max05210238/Infidex_176_V/STL/Lens mount/Classic Cone/CONE_lens_classic_BOARD.stl

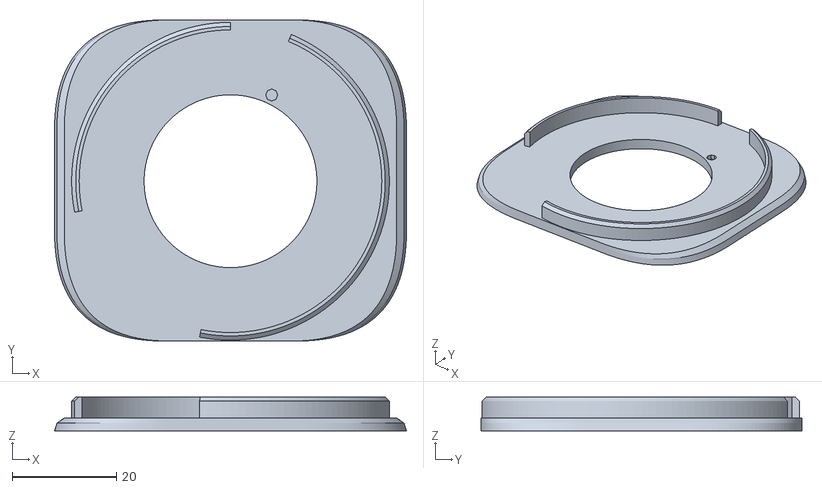
[picture p15: CAD file, 2026-06-08]
STL/Lens mount/Classic Cone/CONE_lens_classic_BOARD.stl
67.6 x 61.7 x 6.50
