max05210238/Infidex_176_V/STL/Lens mount/Focusing Helicoid/Helicoid_FOCUS_ring_ribs_shorter-2mm.stl

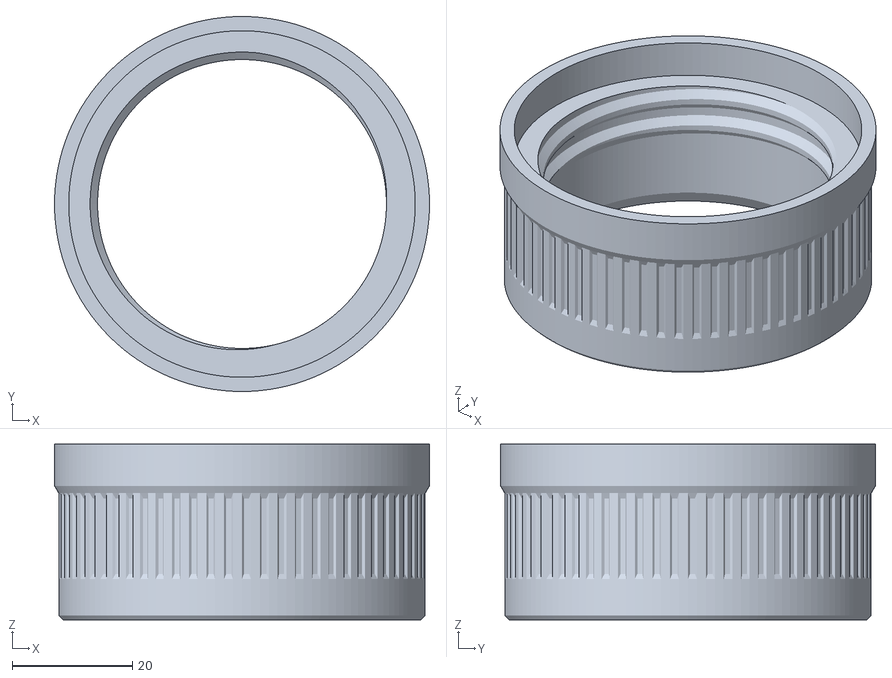
[picture p16: CAD file, 2026-06-08]
STL/Lens mount/Focusing Helicoid/Helicoid_FOCUS_ring_ribs_shorter-2mm.stl
62.4 x 62.4 x 29.2
