max05210238/Infidex_176_V/STL/Lens mount/Tube/Tube_Lens_BOARD.stl

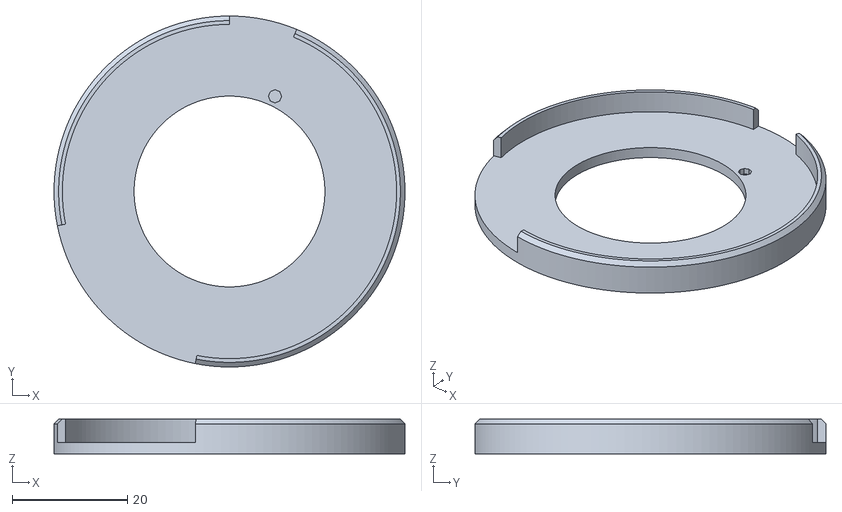
[picture p17: CAD file, 2026-06-08]
STL/Lens mount/Tube/Tube_Lens_BOARD.stl
61.0 x 61.0 x 6.00
