max05210238/Infidex_176_V/MODS/stl/Helicoid_MOUNT_BASE.stl

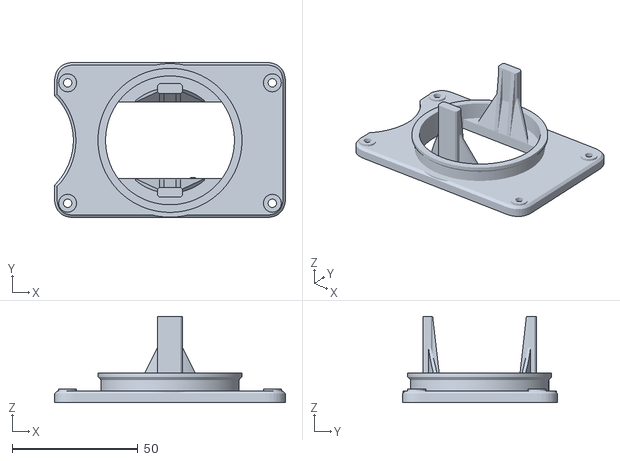
[picture p19: CAD file, 2026-06-08]
MODS/stl/Helicoid_MOUNT_BASE.stl
91.8 x 61.7 x 34.2
