max05210238/Infidex_176_V/STL/Body/BODY_top_ver2.stl

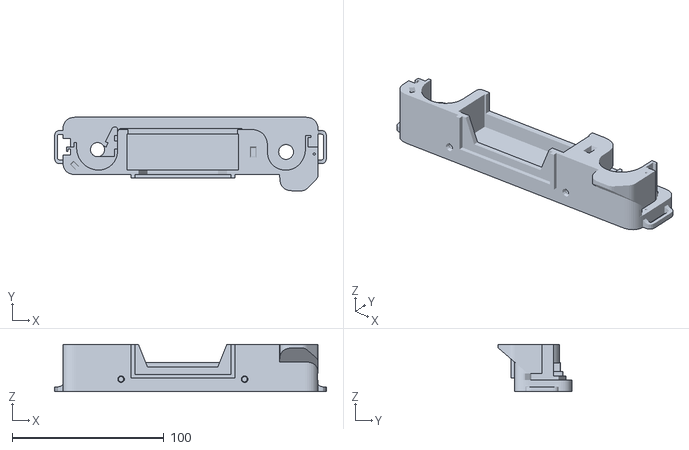
[picture p20: CAD file, 2026-06-08]
STL/Body/BODY_top_ver2.stl
179.0 x 48.5 x 31.0
