max05210238/Infidex_176_V/STL/Lens mount/Focusing Helicoid/Helicoid_INNER_ring_55mm (+0.5mm).stl

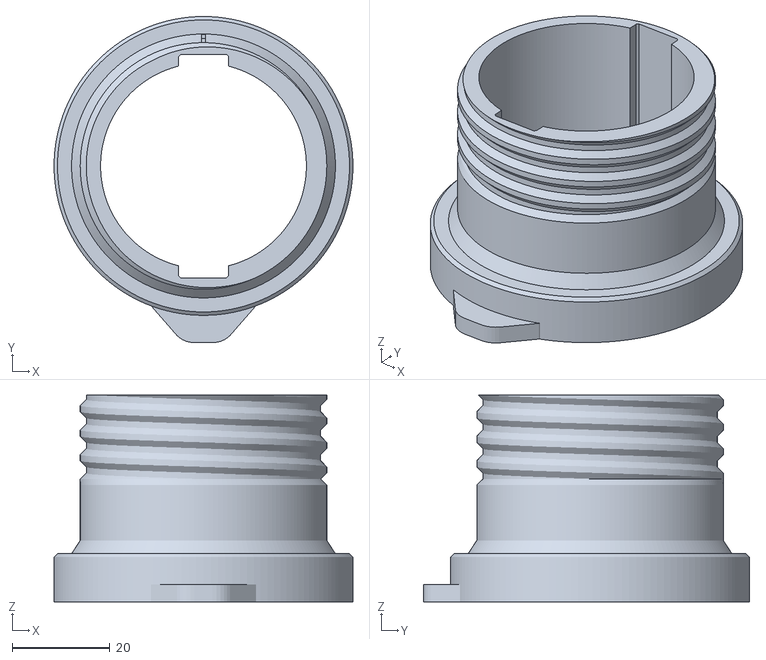
[picture p21: CAD file, 2026-06-08]
STL/Lens mount/Focusing Helicoid/Helicoid_INNER_ring_55mm (+0.5mm).stl
61.0 x 66.5 x 42.2
