max05210238/Infidex_176_V/STL/Small parts/Sprocket_gear_COUNTER.stl

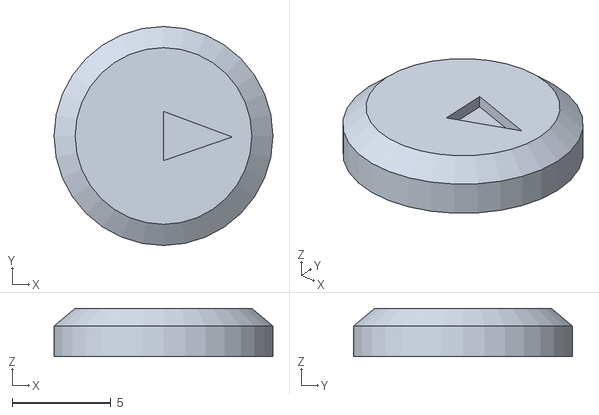
[picture p22: CAD file, 2026-06-08]
STL/Small parts/Sprocket_gear_COUNTER.stl
11.1 x 11.1 x 2.45
