max05210238/Infidex_176_V/MODS/stl/Door_v4.stl

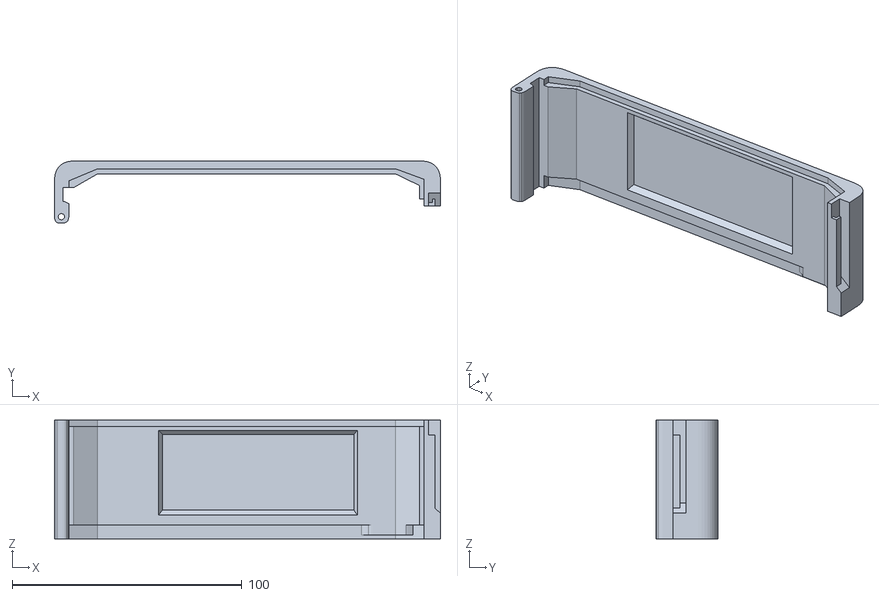
[picture p23: CAD file, 2026-06-08]
MODS/stl/Door_v4.stl
168.0 x 27.0 x 51.7
