max05210238/Infidex_176_V/STL/Body/BODY_bottom_ver2.stl

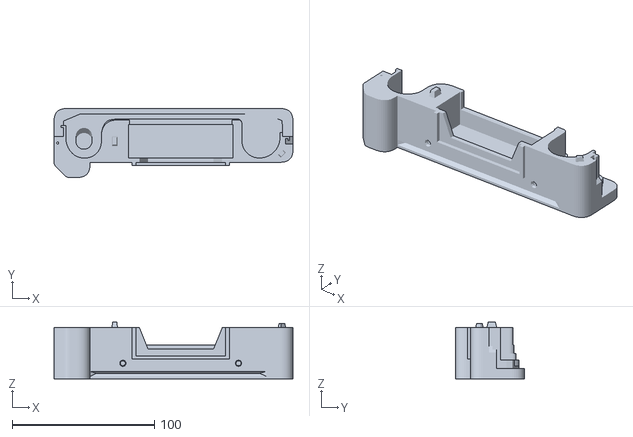
[picture p24: CAD file, 2026-06-08]
STL/Body/BODY_bottom_ver2.stl
168.0 x 48.5 x 40.0
