max05210238/Infidex_176_V/STL/Small parts/Viewfinder_var1_with_text.stl

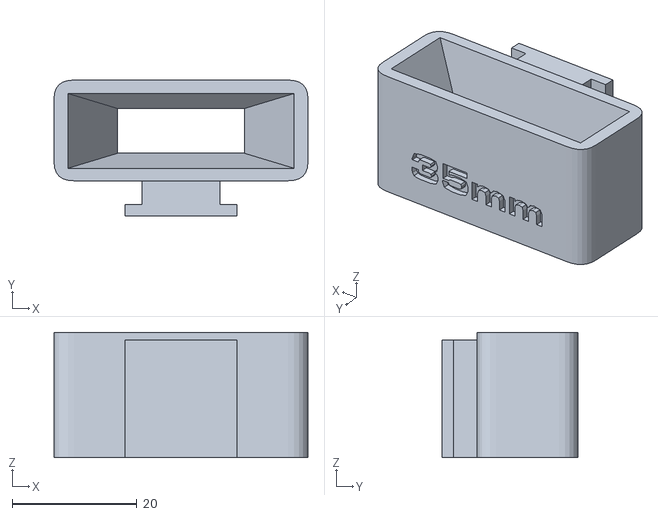
[picture p25: CAD file, 2026-06-08]
STL/Small parts/Viewfinder_var1_with_text.stl
40.7 x 21.8 x 20.1
