max05210238/Infidex_176_V/STL/Lens mount/Focusing Helicoid/Helicoid_FOCUS_ring_ribs.stl

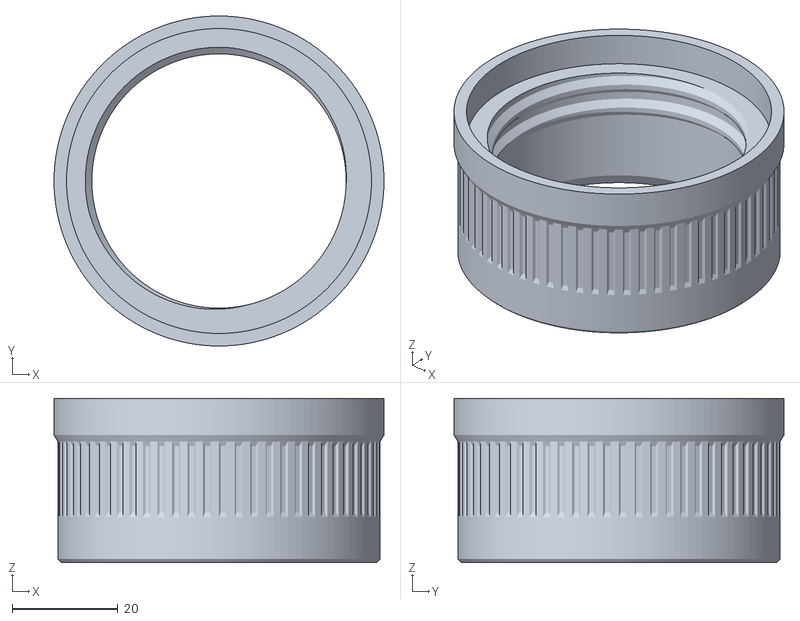
[picture p26: CAD file, 2026-06-08]
STL/Lens mount/Focusing Helicoid/Helicoid_FOCUS_ring_ribs.stl
62.4 x 62.4 x 31.1
