max05210238/Infidex_176_V/STL/Small parts/Winding_knob_var2.stl

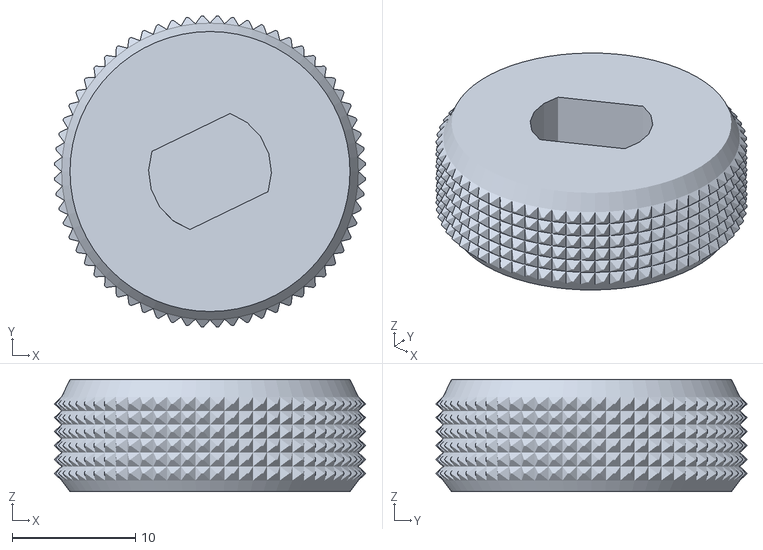
[picture p27: CAD file, 2026-06-08]
STL/Small parts/Winding_knob_var2.stl
25.2 x 25.2 x 9.10
