max05210238/Infidex_176_V/MODS/stl/Body_bottom.stl

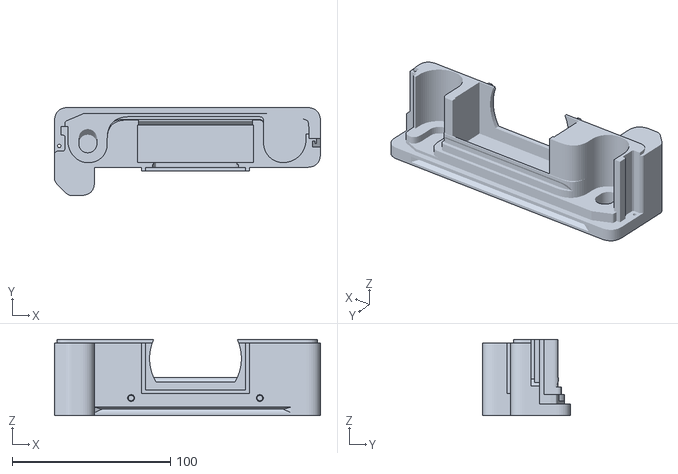
[picture p28: CAD file, 2026-06-08]
MODS/stl/Body_bottom.stl
168.0 x 55.6 x 48.0
