max05210238/Infidex_176_V/STL/Body/Door_var3.stl

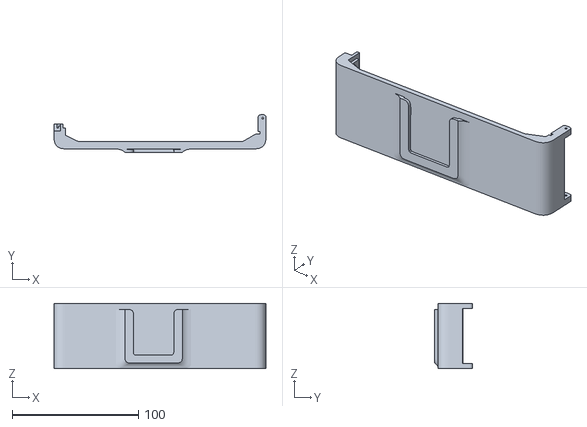
[picture p29: CAD file, 2026-06-08]
STL/Body/Door_var3.stl
168.0 x 29.8 x 51.7
