max05210238/Infidex_176_V/STL/Lens mount/Focusing Helicoid/Helicoid_INNER_ring_80mm_shorter-2mm.stl

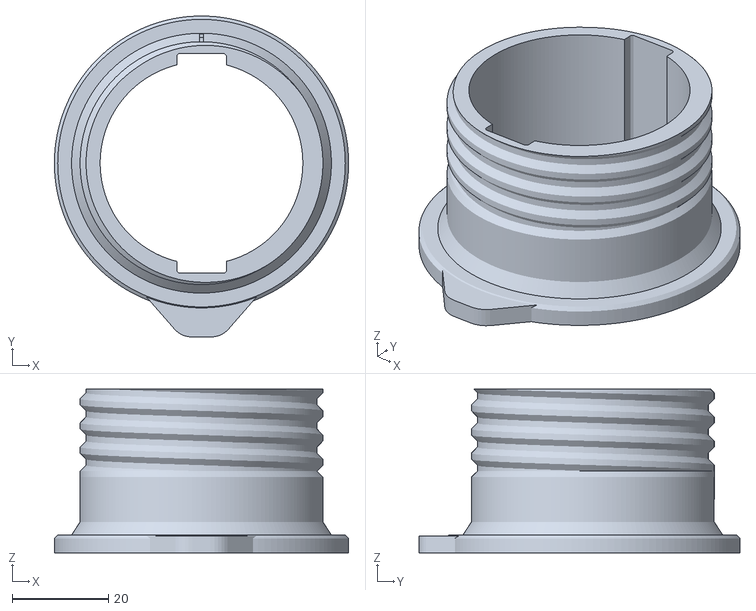
[picture p30: CAD file, 2026-06-08]
STL/Lens mount/Focusing Helicoid/Helicoid_INNER_ring_80mm_shorter-2mm.stl
61.0 x 66.5 x 34.0
