max05210238/Infidex_176_V/STL/Small parts/Latch.stl

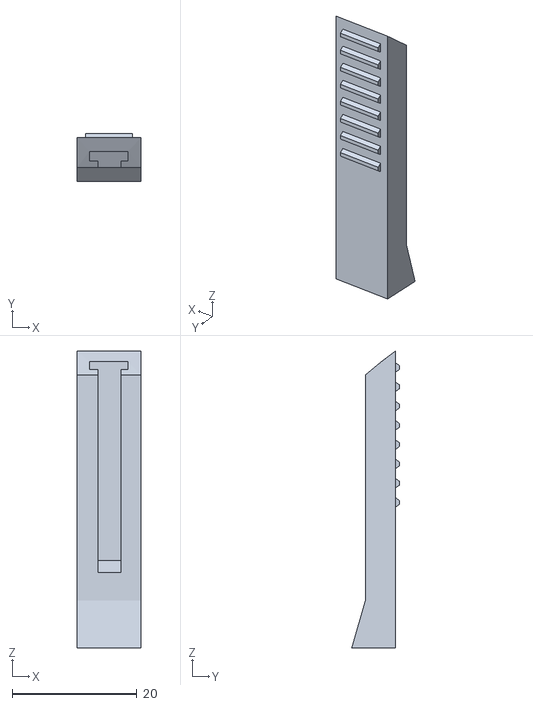
[picture p31: CAD file, 2026-06-08]
STL/Small parts/Latch.stl
10.3 x 7.64 x 47.6
