max05210238/Infidex_176_V/STL/Body/Door_var1.stl

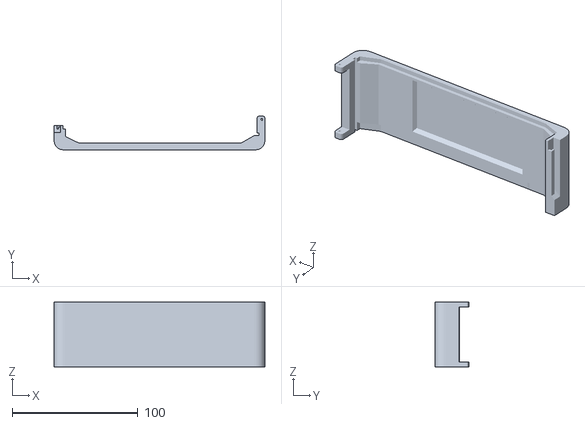
[picture p32: CAD file, 2026-06-08]
STL/Body/Door_var1.stl
168.0 x 27.0 x 51.7
