max05210238/Infidex_176_V/STL/Lens mount/Focusing Helicoid/Helicoid_FIX_ring.stl

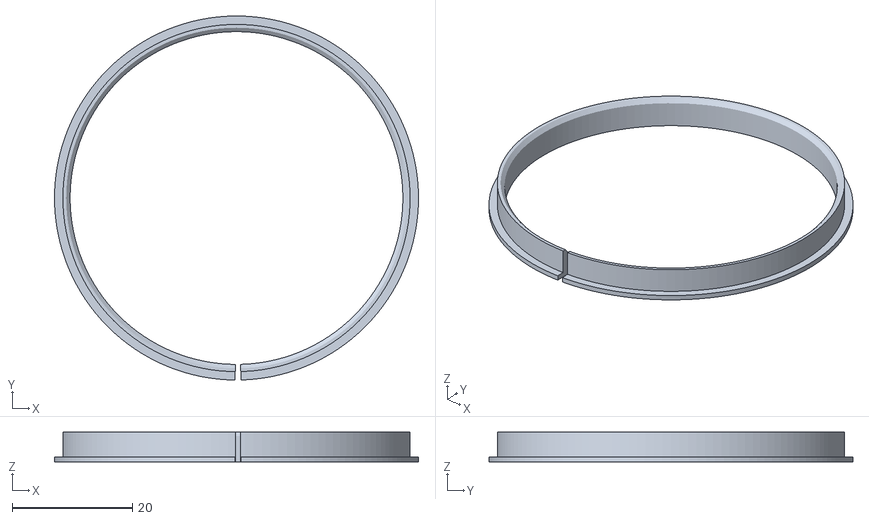
[picture p33: CAD file, 2026-06-08]
STL/Lens mount/Focusing Helicoid/Helicoid_FIX_ring.stl
60.6 x 60.6 x 4.99
