max05210238/Infidex_176_V/STL/Small parts/Lens_Hood_Mamiya_Sekor_80mm_var2.stl

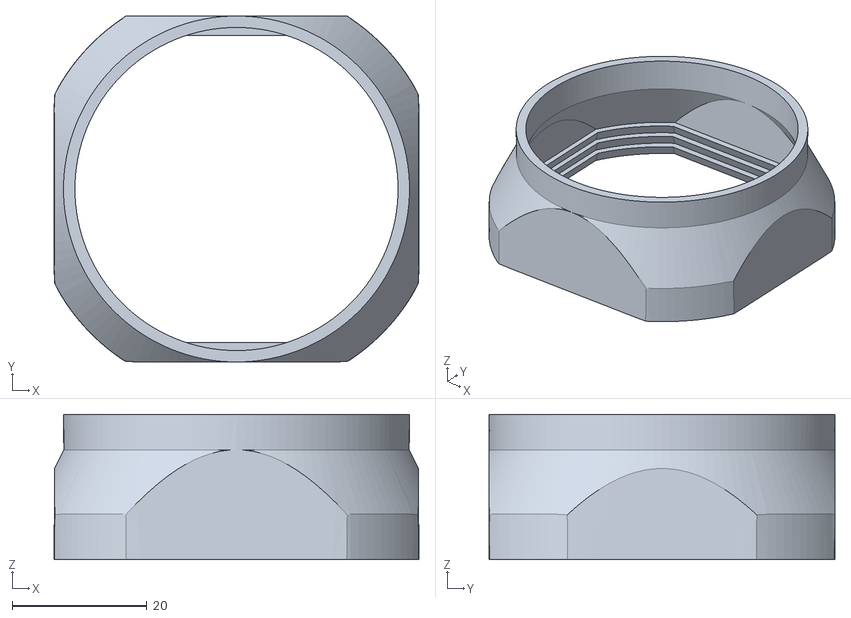
[picture p34: CAD file, 2026-06-08]
STL/Small parts/Lens_Hood_Mamiya_Sekor_80mm_var2.stl
54.2 x 51.4 x 21.6
