max05210238/Infidex_176_V/STL/Small parts/Soviet_35mm_viefinder_lens_MASK.stl

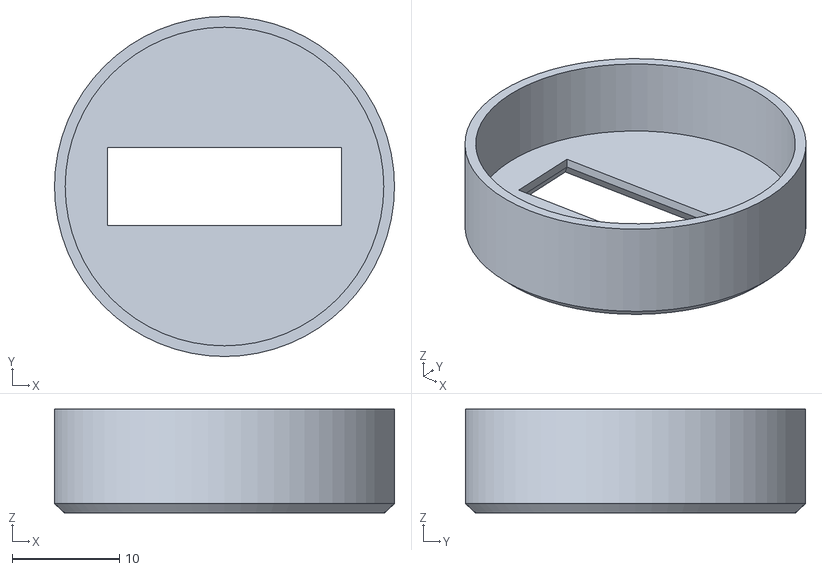
[picture p35: CAD file, 2026-06-08]
STL/Small parts/Soviet_35mm_viefinder_lens_MASK.stl
31.8 x 31.8 x 9.69
