max05210238/Infidex_176_V/STL/Body/Door_var4.stl

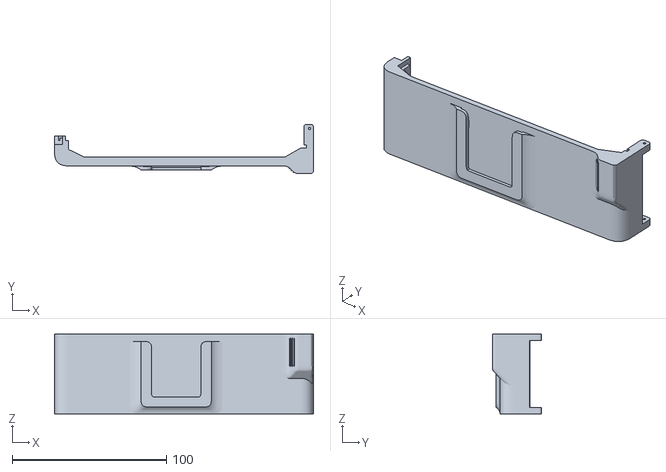
[picture p36: CAD file, 2026-06-08]
STL/Body/Door_var4.stl
168.0 x 32.1 x 51.7
