max05210238/Infidex_176_V/STL/Small parts/Pressure_plate.stl

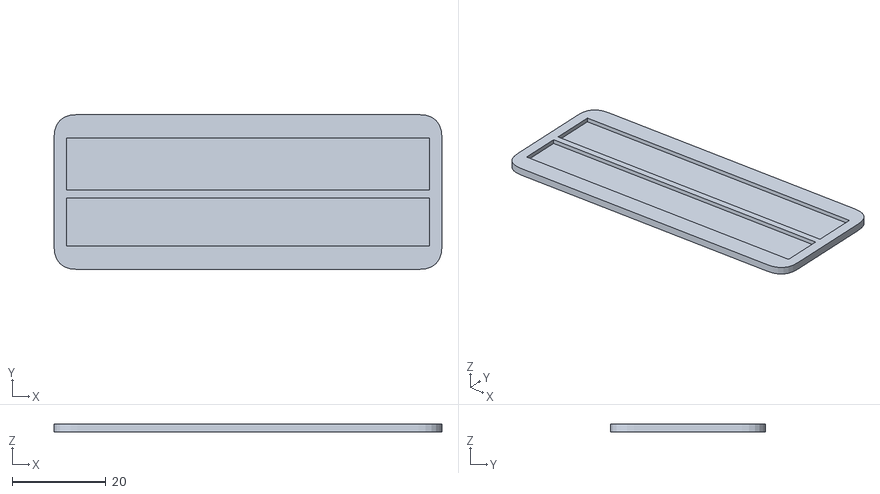
[picture p37: CAD file, 2026-06-08]
STL/Small parts/Pressure_plate.stl
82.8 x 33.0 x 1.77
