max05210238/Infidex_176_V/STL/Lens mount/Focusing Helicoid/Helicoid_Lens_BOARD_lower.stl

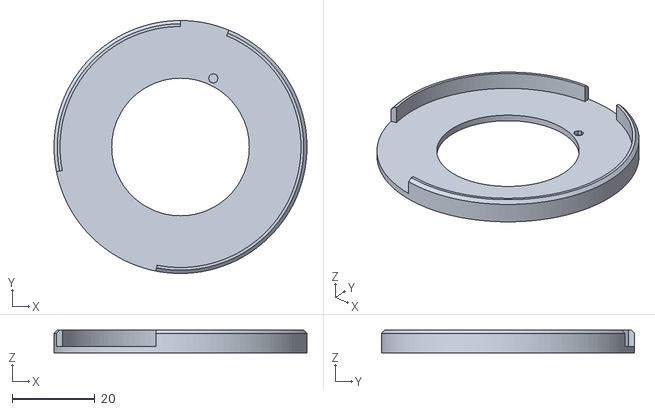
[picture p38: CAD file, 2026-06-08]
STL/Lens mount/Focusing Helicoid/Helicoid_Lens_BOARD_lower.stl
61.0 x 61.0 x 5.50
