max05210238/Infidex_176_V/STL/Small parts/Take_up_spool_MOUNT.stl

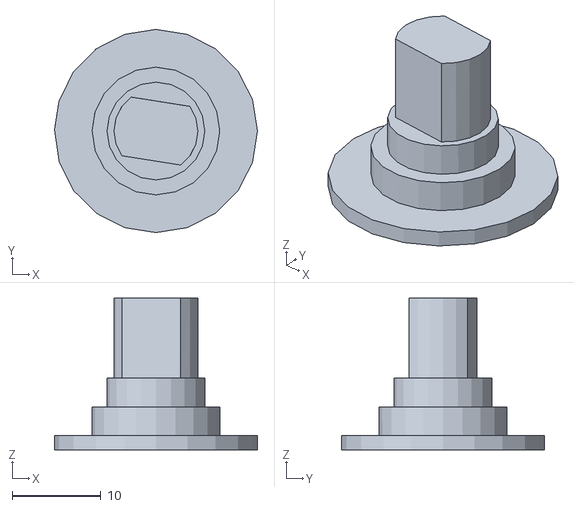
[picture p39: CAD file, 2026-06-08]
STL/Small parts/Take_up_spool_MOUNT.stl
22.8 x 22.9 x 17.1
