max05210238/Infidex_176_V/STL/Lens mount/Focusing Helicoid/Helicoid_INNER_ring_for_55mm_lens.stl

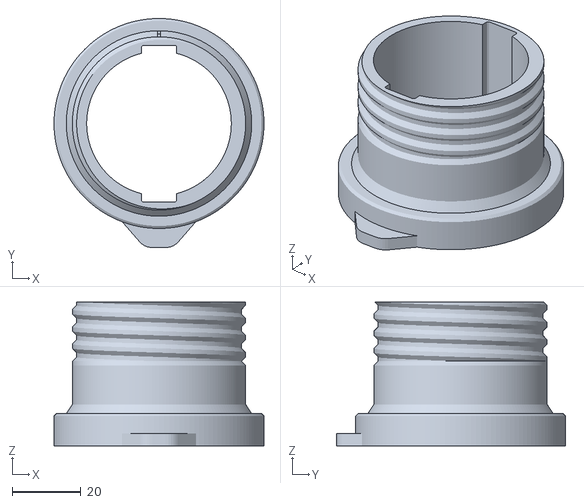
[picture p40: CAD file, 2026-06-08]
STL/Lens mount/Focusing Helicoid/Helicoid_INNER_ring_for_55mm_lens.stl
61.0 x 66.5 x 41.7
