max05210238/Infidex_176_V/STL/Small parts/Winding_knob_var1.stl

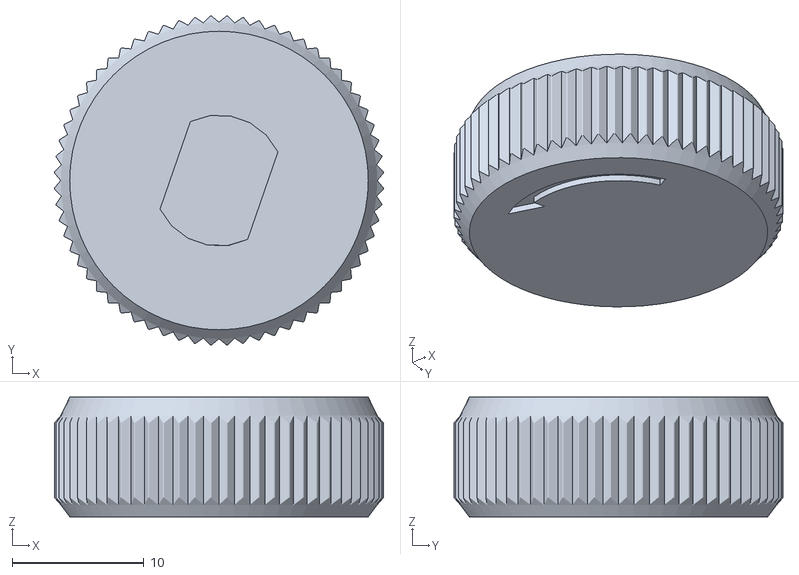
[picture p41: CAD file, 2026-06-08]
STL/Small parts/Winding_knob_var1.stl
25.0 x 25.0 x 9.10
