max05210238/Infidex_176_V/STL/Small parts/Release_cable_plate_FOR_CONE.stl

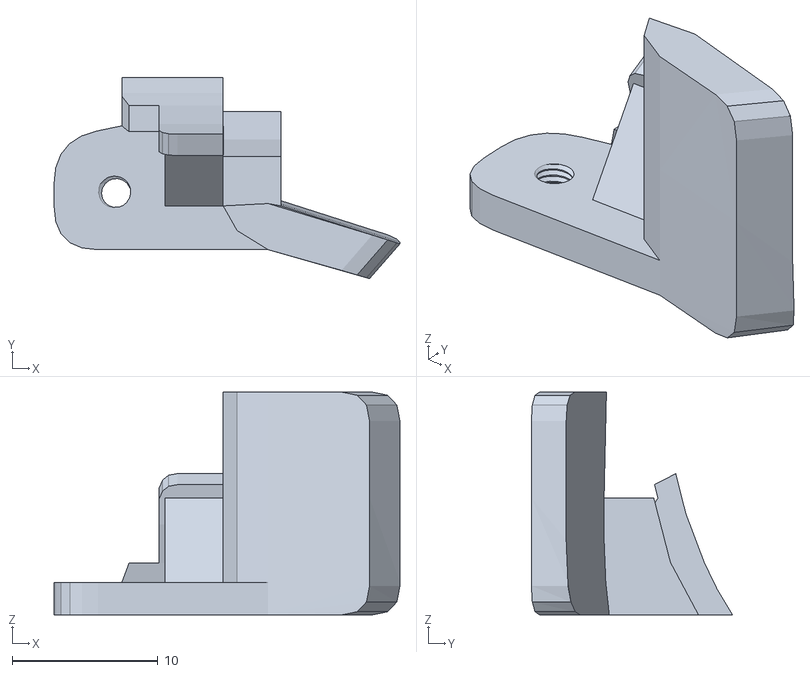
[picture p43: CAD file, 2026-06-08]
STL/Small parts/Release_cable_plate_FOR_CONE.stl
23.7 x 13.8 x 15.3
