max05210238/Infidex_176_V/STL/Small parts/Release_lever_knob.stl

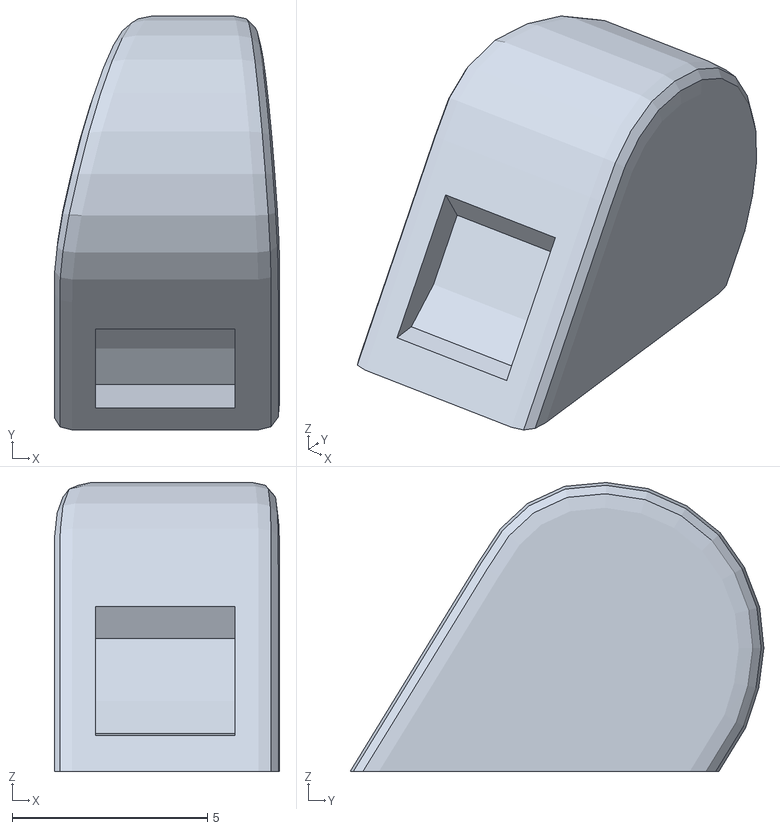
[picture p44: CAD file, 2026-06-08]
STL/Small parts/Release_lever_knob.stl
5.77 x 10.6 x 7.40
