max05210238/Infidex_176_V/STL/Small parts/Release_cable_plate_FOR_HELICOID.stl

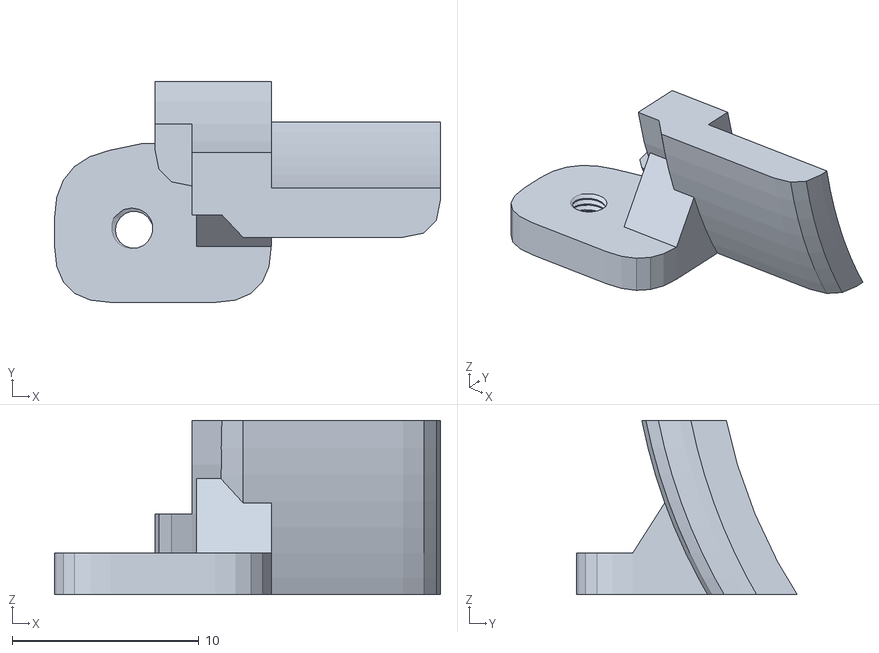
[picture p46: CAD file, 2026-06-08]
STL/Small parts/Release_cable_plate_FOR_HELICOID.stl
20.6 x 11.8 x 9.33
