max05210238/Infidex_176_V/STL/Small parts/Rewinding_knob_var1.stl

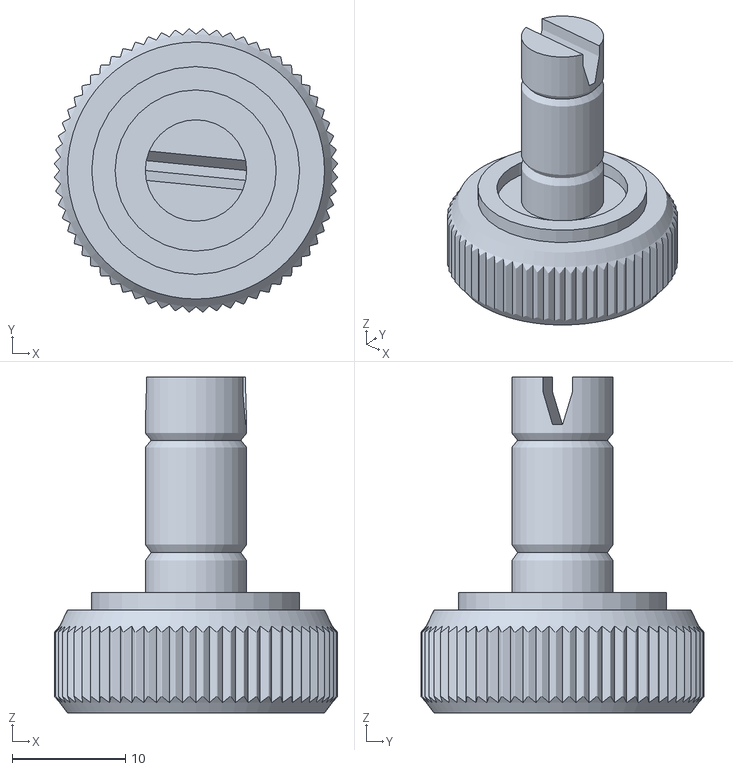
[picture p47: CAD file, 2026-06-08]
STL/Small parts/Rewinding_knob_var1.stl
25.0 x 25.0 x 29.7
