max05210238/Infidex_176_V/STL/Small parts/Take_up_spool_SHAFT.stl

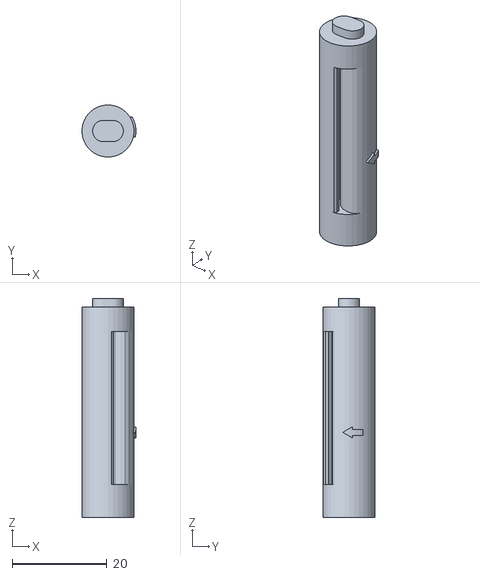
[picture p49: CAD file, 2026-06-08]
STL/Small parts/Take_up_spool_SHAFT.stl
11.4 x 11.0 x 46.2
