max05210238/Infidex_176_V/STL/Small parts/Cold_shoe.stl

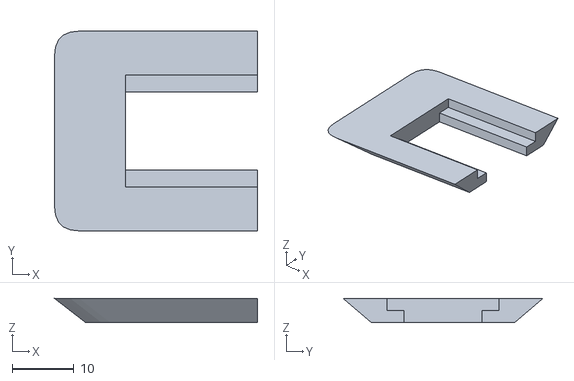
[picture p50: CAD file, 2026-06-08]
STL/Small parts/Cold_shoe.stl
33.0 x 32.4 x 3.91
