max05210238/Infidex_176_V/STL/Small parts/Sprocket_gear_SHAFT.stl

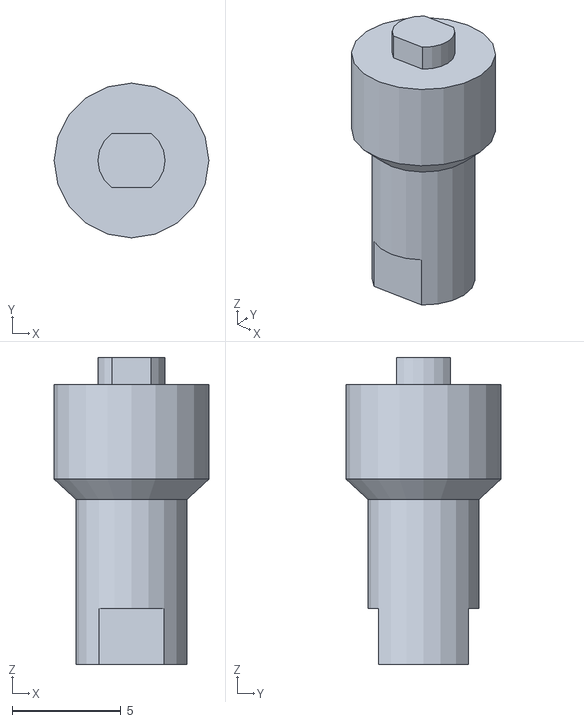
[picture p51: CAD file, 2026-06-08]
STL/Small parts/Sprocket_gear_SHAFT.stl
7.12 x 7.12 x 14.1
