max05210238/Infidex_176_V/STL/Small parts/LensCap_for80mm_v1.stl

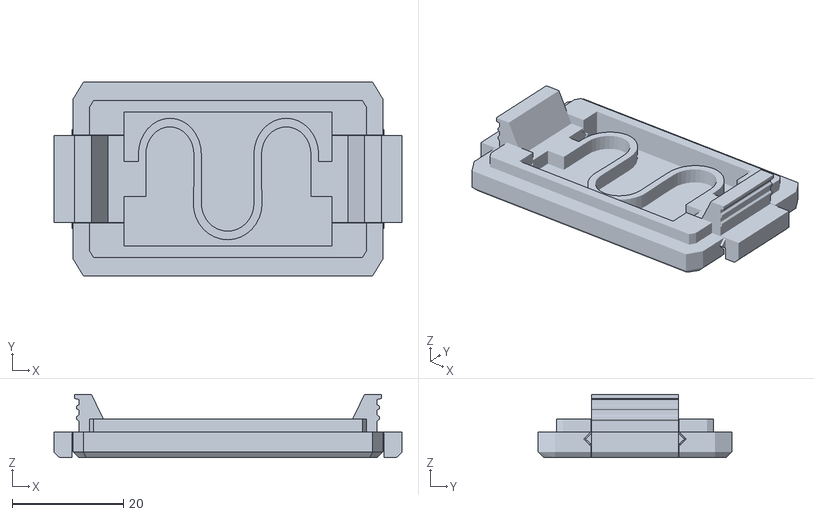
[picture p52: CAD file, 2026-06-08]
STL/Small parts/LensCap_for80mm_v1.stl
62.6 x 34.8 x 11.4
